akaFunk/BlinkyBar/main_pcb_front/main_pcb_front.png

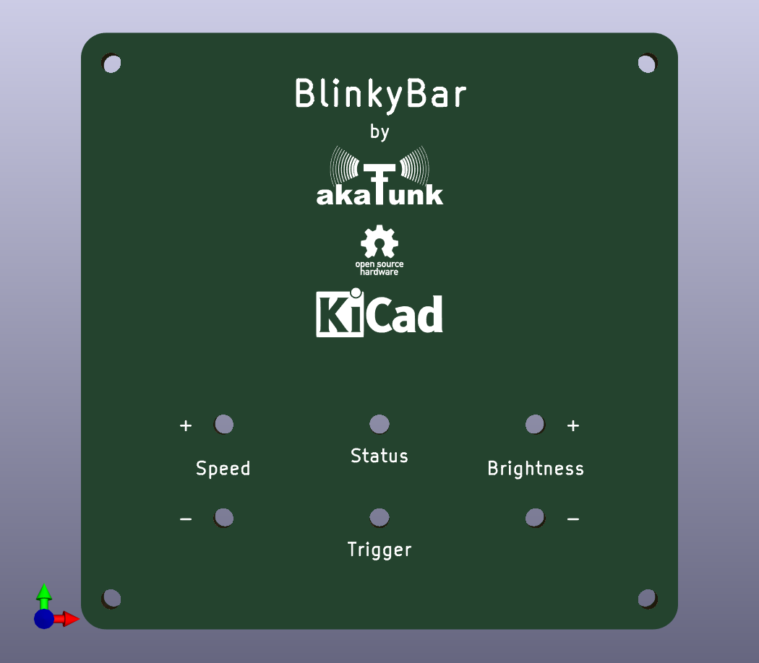
main_pcb_front/main_pcb_front.png
