akaFunk/BlinkyBar/main_pcb_ui/main_pcb_ui.png

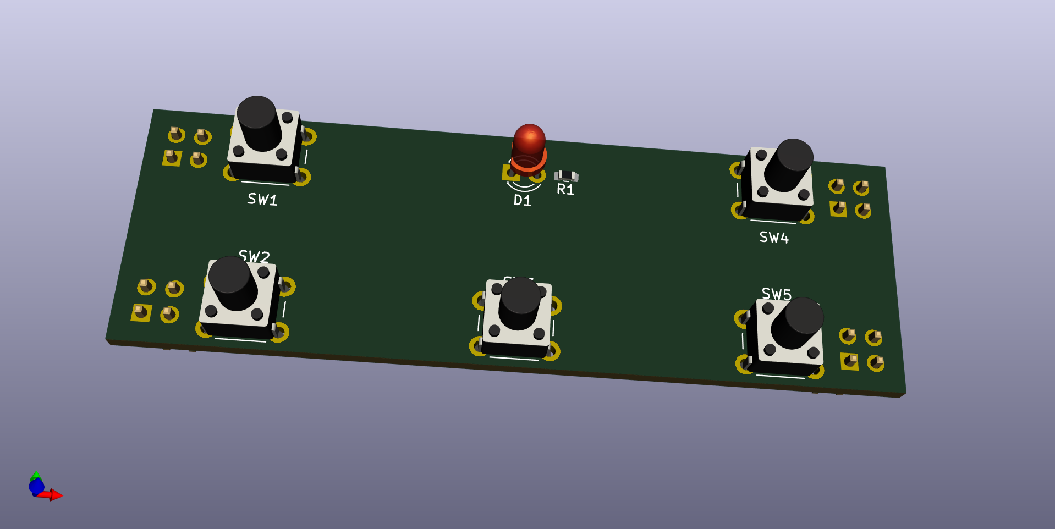
main_pcb_ui/main_pcb_ui.png
