akaFunk/BlinkyBar/server/image.png

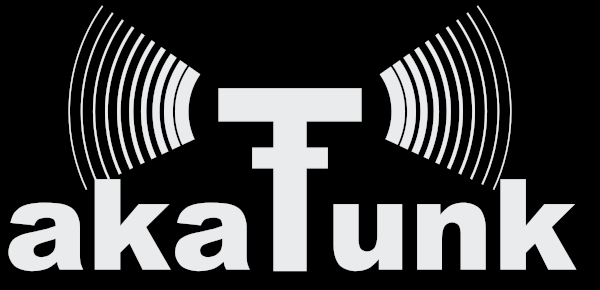
server/image.png
