akaFunk/BlinkyBar/server/colortemperaturetable.py

# Intialize color temperature table
color_temperature_table = {
    1000: (255,  51,   0),
    1100: (255,  69,   0),
    1200: (255,  82,   0),
    1300: (255,  93,   0),
    1400: (255, 102,   0),
    1500: (255, 111,   0),
    1600: (255, 118,   0),
    1700: (255, 124,   0),
    1800: (255, 130,   0),
    1900: (255, 135,   0),
    2000: (255, 141,  11),
    2100: (255, 146,  29),
    2200: (255, 152,  41),
    2300: (255, 157,  51),
    2400: (255, 162,  60),
    2500: (255, 166,  69),
    2600: (255, 170,  77),
    2700: (255, 174,  84),
    2800: (255, 178,  91),
    2900: (255, 182,  98),
    3000: (255, 185, 105),
    3100: (255, 189, 111),
    3200: (255, 192, 118),
    3300: (255, 195, 124),
    3400: (255, 198, 130),
    3500: (255, 201, 135),
    3600: (255, 203, 141),
    3700: (255, 206, 146),
    3800: (255, 208, 151),
    3900: (255, 211, 156),
    4000: (255, 213, 161),
    4100: (255, 215, 166),
    4200: (255, 217, 171),
    4300: (255, 219, 175),
    4400: (255, 221, 180),
    4500: (255, 223, 184),
    4600: (255, 225, 188),
    4700: (255, 226, 192),
    4800: (255, 228, 196),
    4900: (255, 229, 200),
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
}

def get_color_temperatures(temp_sel):
    return color_temperature_table.get(temp_sel) or color_temperature_table[min(color_temperature_table.keys(), key = lambda key: abs(key-temp_sel))]
